BadenLab/Thunderdome/Images/Coexcitation.png

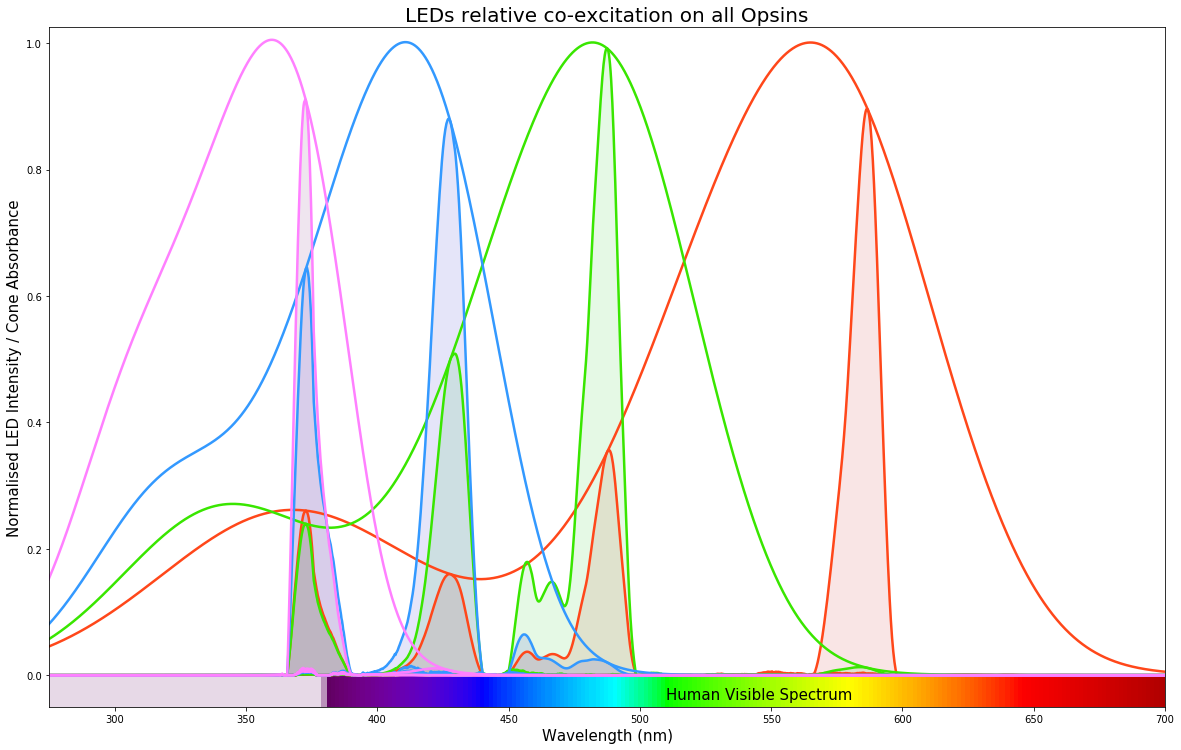
Images/Coexcitation.png
