BadenLab/Thunderdome/Instruction Manual/Stimulator Calibration/Calibration_Figures/LED Energy Flux Nat-Stat.png

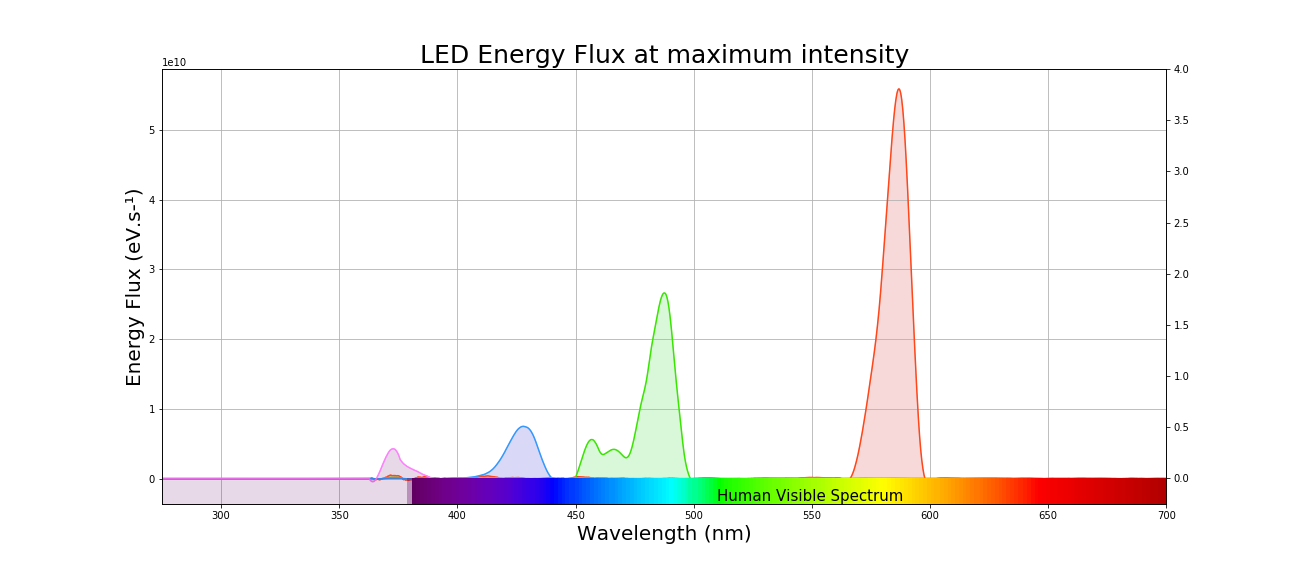
Instruction Manual/Stimulator Calibration/Calibration_Figures/LED Energy Flux Nat-Stat.png
