BadenLab/Thunderdome/Instruction Manual/Stimulator Calibration/Calibration_Figures/LED Energy Flux.png

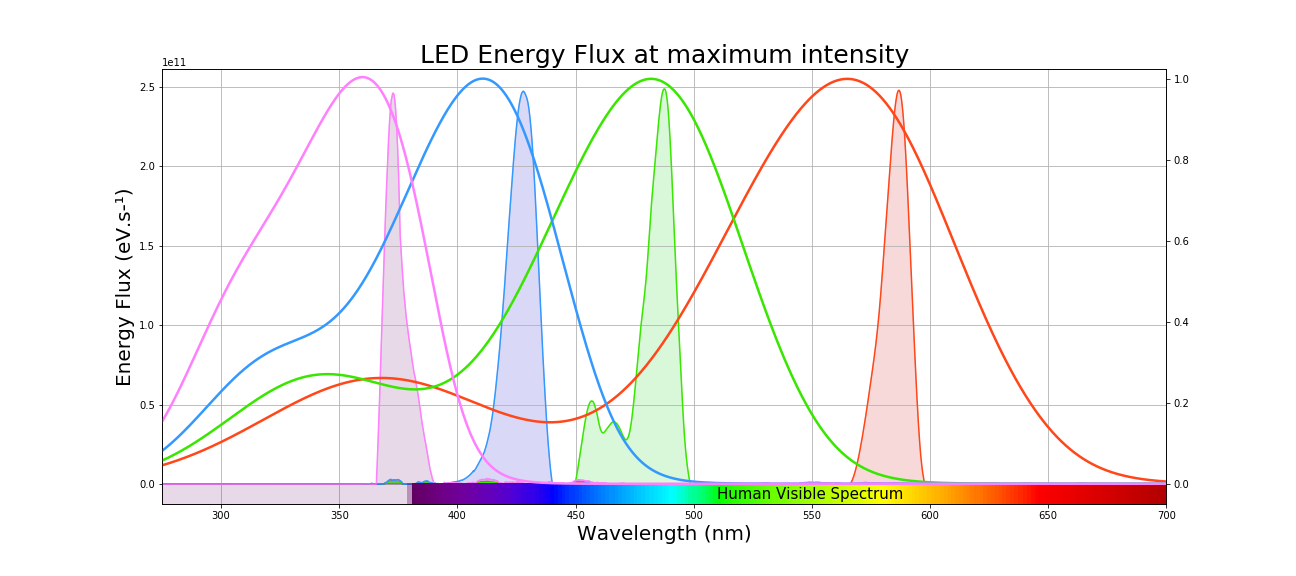
Instruction Manual/Stimulator Calibration/Calibration_Figures/LED Energy Flux.png
