BadenLab/Thunderdome/Instruction Manual/Stimulator Calibration/Calibration_Figures/Opsin-LED Photo-Isomerisation Rates Nat-Stat.png

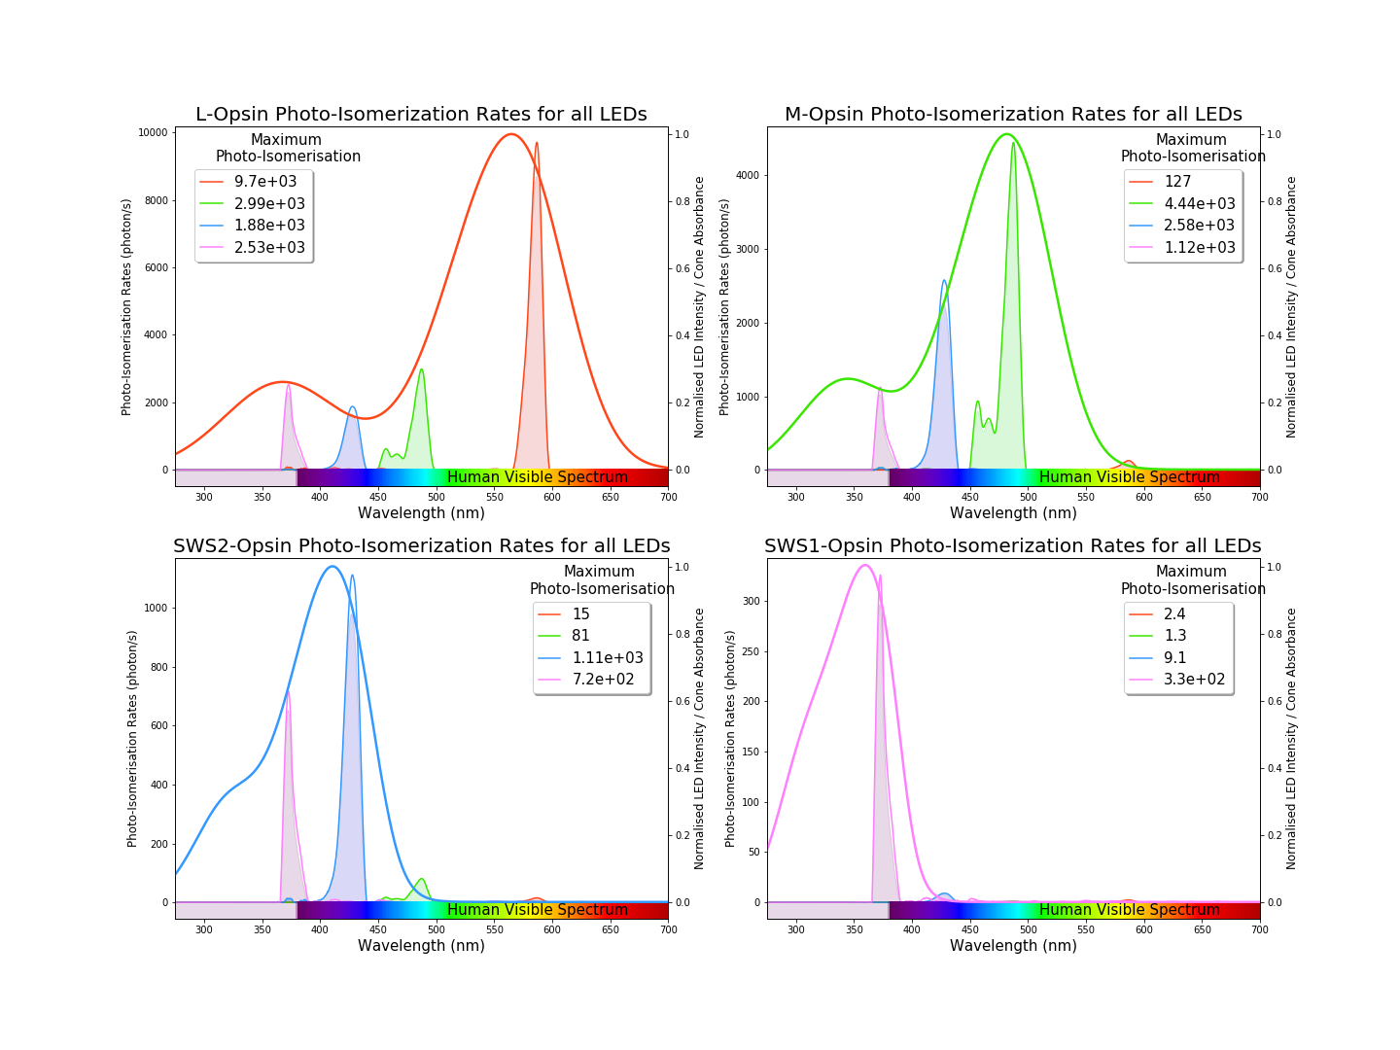
Instruction Manual/Stimulator Calibration/Calibration_Figures/Opsin-LED Photo-Isomerisation Rates Nat-Stat.png
