BadenLab/Thunderdome/Instruction Manual/Stimulator Calibration/Calibration_Figures/Opsin-LED Photo-Isomerisation Rates.png

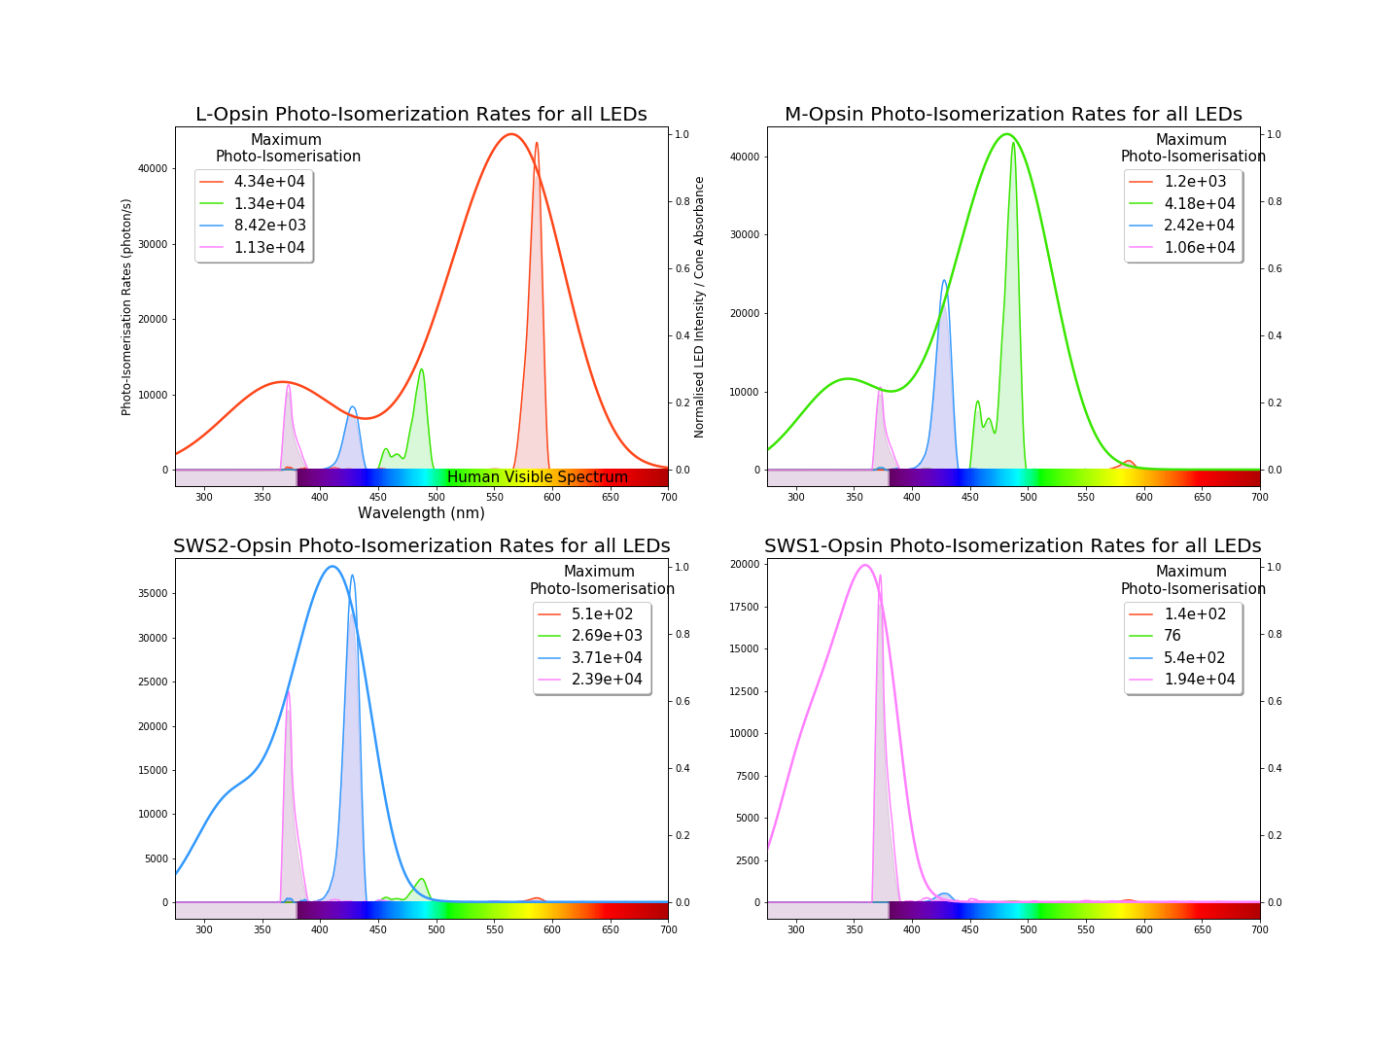
Instruction Manual/Stimulator Calibration/Calibration_Figures/Opsin-LED Photo-Isomerisation Rates.png
