BadenLab/Thunderdome/Instruction Manual/Stimulator Calibration/Calibration_Figures/Photo-Isomerisation Rates Matrix Nat-Stat.png

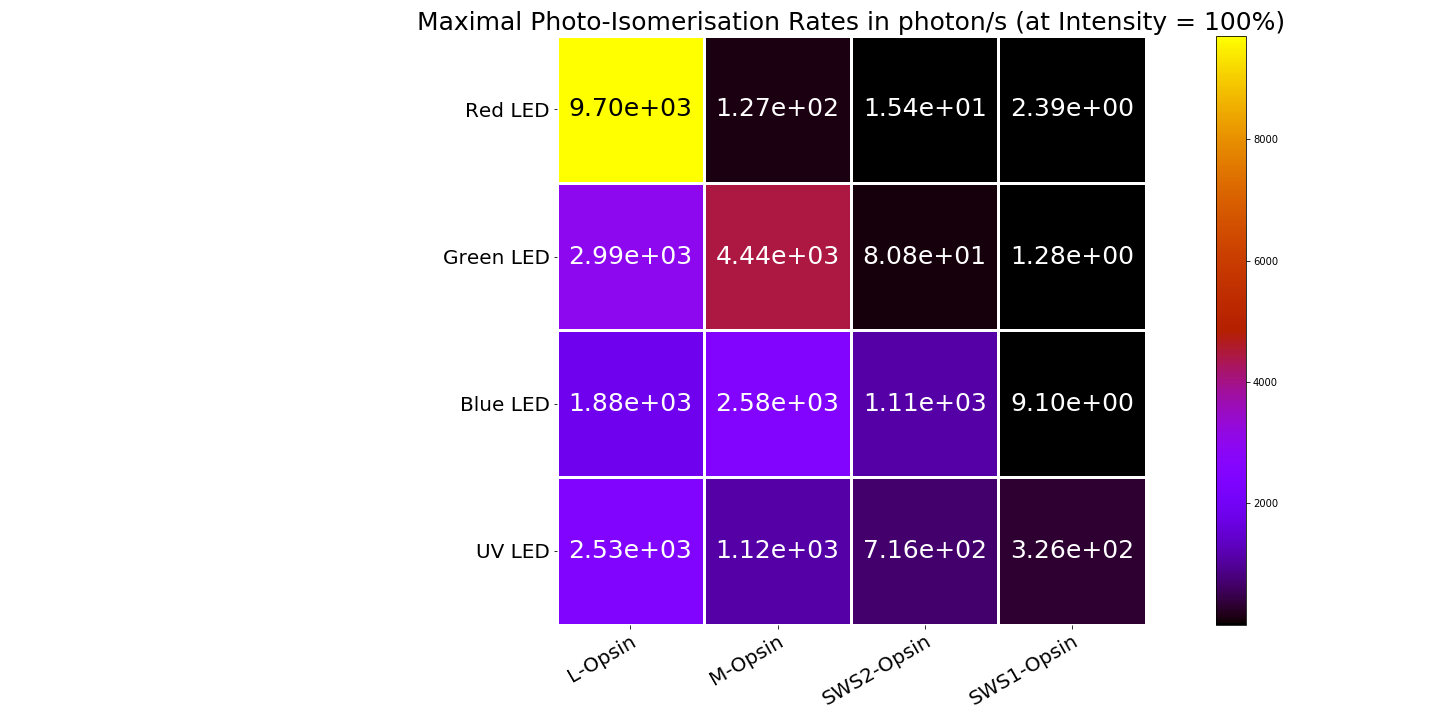
Instruction Manual/Stimulator Calibration/Calibration_Figures/Photo-Isomerisation Rates Matrix Nat-Stat.png
