BadenLab/Thunderdome/Instruction Manual/Stimulator Calibration/Calibration_Figures/Photo-Isomerisation Rates Summary Nat-Stat.png

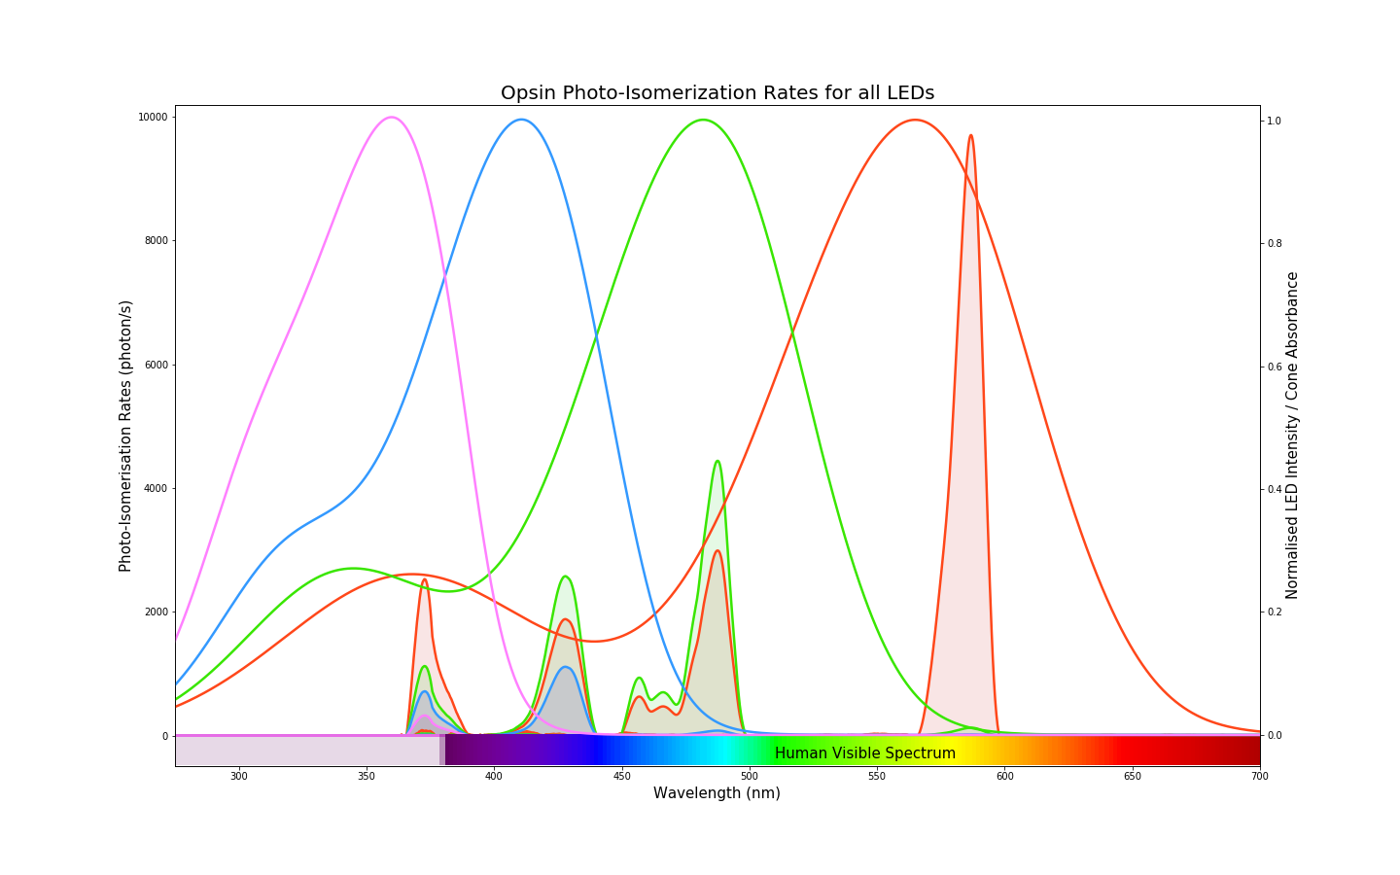
Instruction Manual/Stimulator Calibration/Calibration_Figures/Photo-Isomerisation Rates Summary Nat-Stat.png
