BadenLab/Thunderdome/Instruction Manual/Stimulator Calibration/Calibration_Figures/Photo-Isomerisation Rates Summary.png

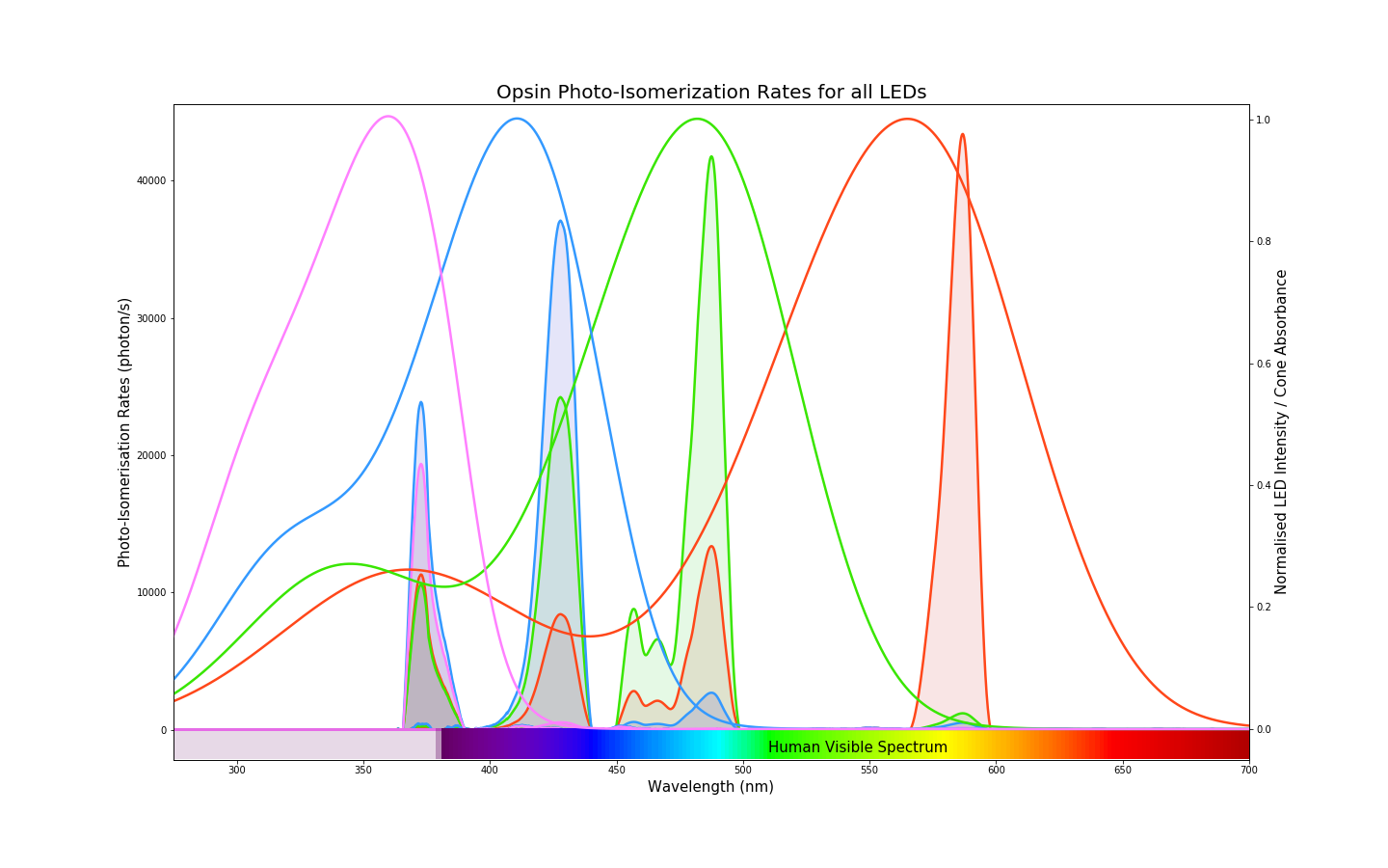
Instruction Manual/Stimulator Calibration/Calibration_Figures/Photo-Isomerisation Rates Summary.png
