BadenLab/Thunderdome/Instruction Manual/Stimulator Calibration/Calibration_Figures/Powermeter Recordings Nat-Stat.png

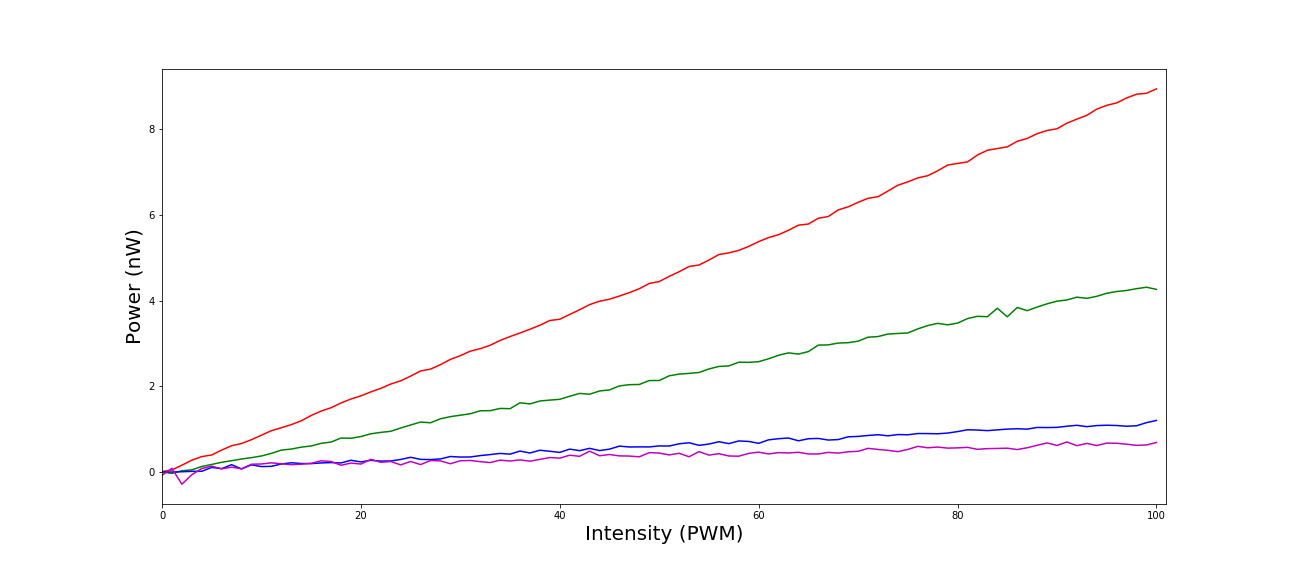
Instruction Manual/Stimulator Calibration/Calibration_Figures/Powermeter Recordings Nat-Stat.png
