BadenLab/Thunderdome/Instruction Manual/Stimulator Calibration/Calibration_Figures/Powermeter Recordings Sumary.png

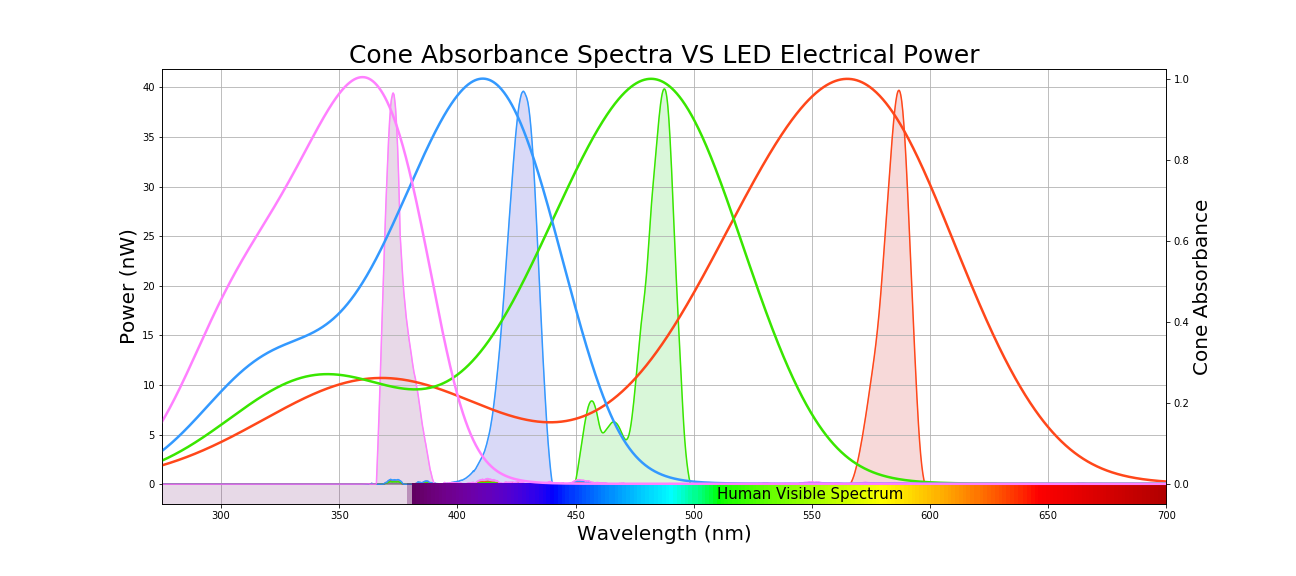
Instruction Manual/Stimulator Calibration/Calibration_Figures/Powermeter Recordings Sumary.png
