BadenLab/Thunderdome/Instruction Manual/Stimulator Calibration/Calibration_Figures/Relative Co-Excitation Matrix.png

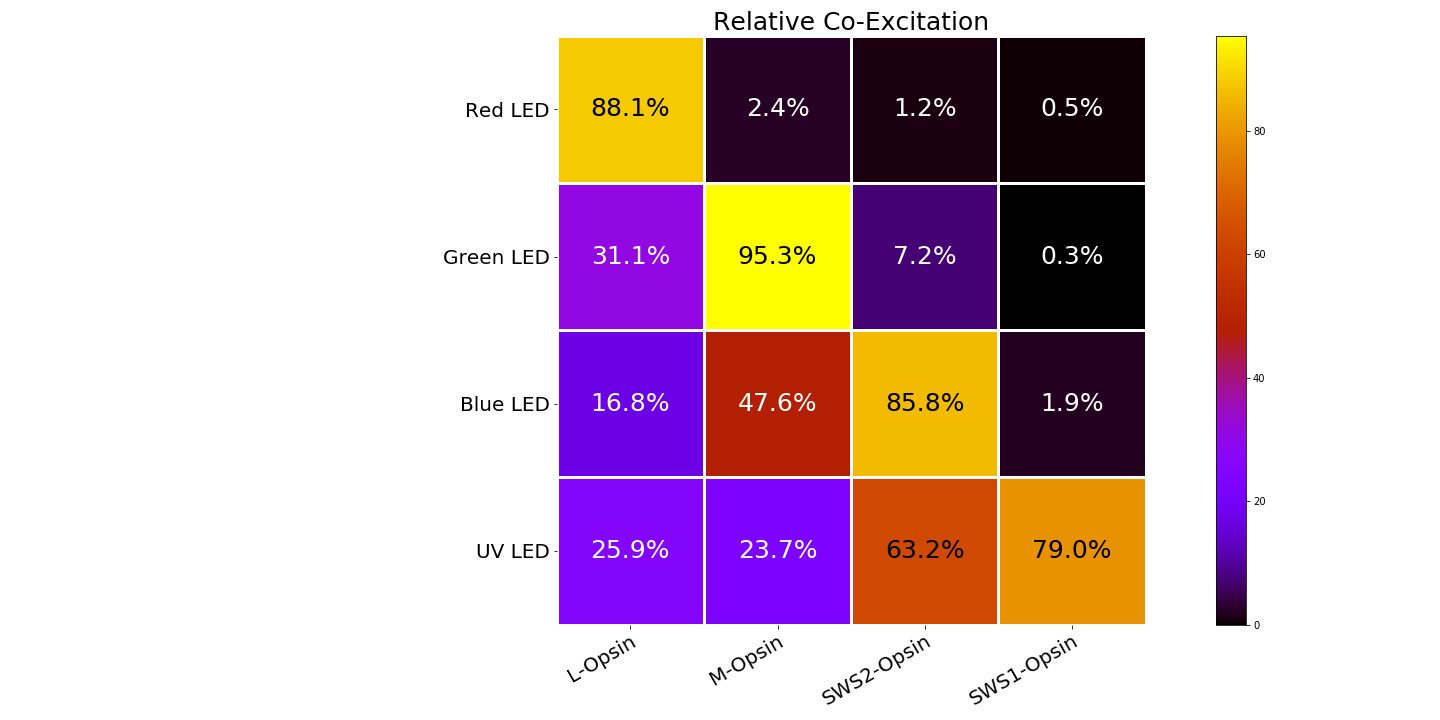
Instruction Manual/Stimulator Calibration/Calibration_Figures/Relative Co-Excitation Matrix.png
