BadenLab/Thunderdome/Arduino Code/V2.3/LED_Values.h

int            R_0_N          = 0;
int            R_0_NE         = 1;
int            R_0_E          = 2;
int            R_0_SE         = 3;
int            R_0_S          = 4;
int            R_0_SW         = 5;
int            R_0_W          = 6;
int            R_0_NW         = 7;
int            R_30_N         = 8;
int            R_30_NE        = 9;
int            R_30_E         = 10;
int            R_30_SE        = 11;
int            R_30_S         = 12;
int            R_30_SW        = 13;
int            R_30_W         = 14;
int            R_30_NW        = 15;
int            R_60_N         = 16;
int            R_60_NE        = 17;
int            R_60_E         = 18;
int            R_60_SE        = 19;
int            R_60_S         = 20;
int            R_60_SW        = 21;
int            R_60_W         = 22;
int            R_60_NW        = 23;

int            G_0_N          = 0 + 24;
int            G_0_NE         = 1 + 24;
int            G_0_E          = 2 + 24;
int            G_0_SE         = 3 + 24;
int            G_0_S          = 4 + 24;
int            G_0_SW         = 5 + 24;
int            G_0_W          = 6 + 24;
int            G_0_NW         = 7 + 24;
int            G_30_N         = 8 + 24;
int            G_30_NE        = 9 + 24;
int            G_30_E         = 10 + 24;
int            G_30_SE        = 11 + 24;
int            G_30_S         = 12 + 24;
int            G_30_SW        = 13 + 24;
int            G_30_W         = 14 + 24;
int            G_30_NW        = 15 + 24;
int            G_60_N         = 16 + 24;
int            G_60_NE        = 17 + 24;
int            G_60_E         = 18 + 24;
int            G_60_SE        = 19 + 24;
int            G_60_S         = 20 + 24;
int            G_60_SW        = 21 + 24;
int            G_60_W         = 22 + 24;
int            G_60_NW        = 23 + 24;

int            B_0_N          = 0 + 2*24;
int            B_0_NE         = 1 + 2*24;
int            B_0_E          = 2 + 2*24;
int            B_0_SE         = 3 + 2*24;
int            B_0_S          = 4 + 2*24;
int            B_0_SW         = 5 + 2*24;
int            B_0_W          = 6 + 2*24;
int            B_0_NW         = 7 + 2*24;
int            B_30_N         = 8 + 2*24;
int            B_30_NE        = 9 + 2*24;
int            B_30_E         = 10 + 2*24;
int            B_30_SE        = 11 + 2*24;
int            B_30_S         = 12 + 2*24;
int            B_30_SW        = 13 + 2*24;
int            B_30_W         = 14 + 2*24;
int            B_30_NW        = 15 + 2*24;
int            B_60_N         = 16 + 2*24;
int            B_60_NE        = 17 + 2*24;
int            B_60_E         = 18 + 2*24;
int            B_60_SE        = 19 + 2*24;
int            B_60_S         = 20 + 2*24;
int            B_60_SW        = 21 + 2*24;
int            B_60_W         = 22 + 2*24;
int            B_60_NW        = 23 + 2*24;

int            U_0_N          = 0 + 3*24;
int            U_0_NE         = 1 + 3*24;
int            U_0_E          = 2 + 3*24;
int            U_0_SE         = 3 + 3*24;
int            U_0_S          = 4 + 3*24;
int            U_0_SW         = 5 + 3*24;
int            U_0_W          = 6 + 3*24;
int            U_0_NW         = 7 + 3*24;
int            U_30_N         = 8 + 3*24;
int            U_30_NE        = 9 + 3*24;
int            U_30_E         = 10 + 3*24;
int            U_30_SE        = 11 + 3*24;
int            U_30_S         = 12 + 3*24;
int            U_30_SW        = 13 + 3*24;
int            U_30_W         = 14 + 3*24;
int            U_30_NW        = 15 + 3*24;
int            U_60_N         = 16 + 3*24;
int            U_60_NE        = 17 + 3*24;
int            U_60_E         = 18 + 3*24;
int            U_60_SE        = 19 + 3*24;
int            U_60_S         = 20 + 3*24;
int            U_60_SW        = 21 + 3*24;
int            U_60_W         = 22 + 3*24;
int            U_60_NW        = 23 + 3*24;


//
//array Red_Array ={
//R_0_N, R_0_NE, R_0_E, R_0_SE, R_0_S, R_0_SW, R_0_W, R_0_NW,
//R_30_N, R_30_NE, R_30_E, R_30_SE, R_30_S, R_30_SW, R_30_W, R_30_NW,
//R_60_N, R_60_NE, R_60_E, R_60_SE, R_60_S, R_60_SW, R_60_W, R_60_NW,
//};
//
//array Green_Array ={
//G_0_N, G_0_NE, G_0_E, G_0_SE, G_0_S, G_0_SW, G_0_W, G_0_NW,
//G_30_N, G_30_NE, G_30_E, G_30_SE, G_30_S, G_30_SW, G_30_W, G_30_NW,
//G_60_N, G_60_NE, G_60_E, G_60_SE, G_60_S, G_60_SW, G_60_W, G_60_NW,
//};
//
//array Blue_Array ={
//B_0_N, B_0_NE, B_0_E, B_0_SE, B_0_S, B_0_SW, B_0_W, B_0_NW,
//B_30_N, B_30_NE, B_30_E, B_30_SE, B_30_S, B_30_SW, B_30_W, B_30_NW,
//B_60_N, B_60_NE, B_60_E, B_60_SE, B_60_S, B_60_SW, B_60_W, B_60_NW,
//};
//
//array UV_Array ={
//U_0_N, U_0_NE, U_0_E, U_0_SE, U_0_S, U_0_SW, U_0_W, U_0_NW,
//U_30_N, U_30_NE, U_30_E, U_30_SE, U_30_S, U_30_SW, U_30_W, U_30_NW,
//U_60_N, U_60_NE, U_60_E, U_60_SE, U_60_S, U_60_SW, U_60_W, U_60_NW,
//};
//
//// // // // // // // // // // // // // // // // // // // // // // //
//
//array Red_0_Array ={
//R_0_N, R_0_NE, R_0_E, R_0_SE, R_0_S, R_0_SW, R_0_W, R_0_NW
//};
//
//array Green_0_Array ={
//G_0_N, G_0_NE, G_0_E, G_0_SE, G_0_S, G_0_SW, G_0_W, G_0_NW
//};
//
//array Blue_0_Array ={
//B_0_N, B_0_NE, B_0_E, B_0_SE, B_0_S, B_0_SW, B_0_W, B_0_NW
//};
//
//array UV_0_Array ={
//U_0_N, U_0_NE, U_0_E, U_0_SE, U_0_S, U_0_SW, U_0_W, U_0_NW
//};
//
//// // // // // // // // // // // // // // // // // // // // // // //
//
//array Red_30_Array ={
//R_30_N, R_30_NE, R_30_E, R_30_SE, R_30_S, R_30_SW, R_30_W, R_30_NW
//};
//
//array Green_30_Array ={
//G_30_N, G_30_NE, G_30_E, G_30_SE, G_30_S, G_30_SW, G_30_W, G_30_NW
//};
//
//array Blue_30_Array ={
//B_30_N, B_30_NE, B_30_E, B_30_SE, B_30_S, B_30_SW, B_30_W, B_30_NW
//};
//
//array UV_30_Array ={
//U_30_N, U_30_NE, U_30_E, U_30_SE, U_30_S, U_30_SW, U_30_W, U_30_NW
//};
//
//// // // // // // // // // // // // // // // // // // // // // // //
//
//array Red_60_Array ={
//R_60_N, R_60_NE, R_60_E, R_60_SE, R_60_S, R_60_SW, R_60_W, R_60_NW
//};
//
//array Green_60_Array ={
//G_60_N, G_60_NE, G_60_E, G_60_SE, G_60_S, G_60_SW, G_60_W, G_60_NW
//};
//
//array Blue_60_Array ={
//B_60_N, B_60_NE, B_60_E, B_60_SE, B_60_S, B_60_SW, B_60_W, B_60_NW
//};
//
//array UV_60_Array ={
//U_60_N, U_60_NE, U_60_E, U_60_SE, U_60_S, U_60_SW, U_60_W, U_60_NW
//};
